jp112sdl/WemosD1_HomeMatic_StatusDisplay/Images/config_beispiel.png

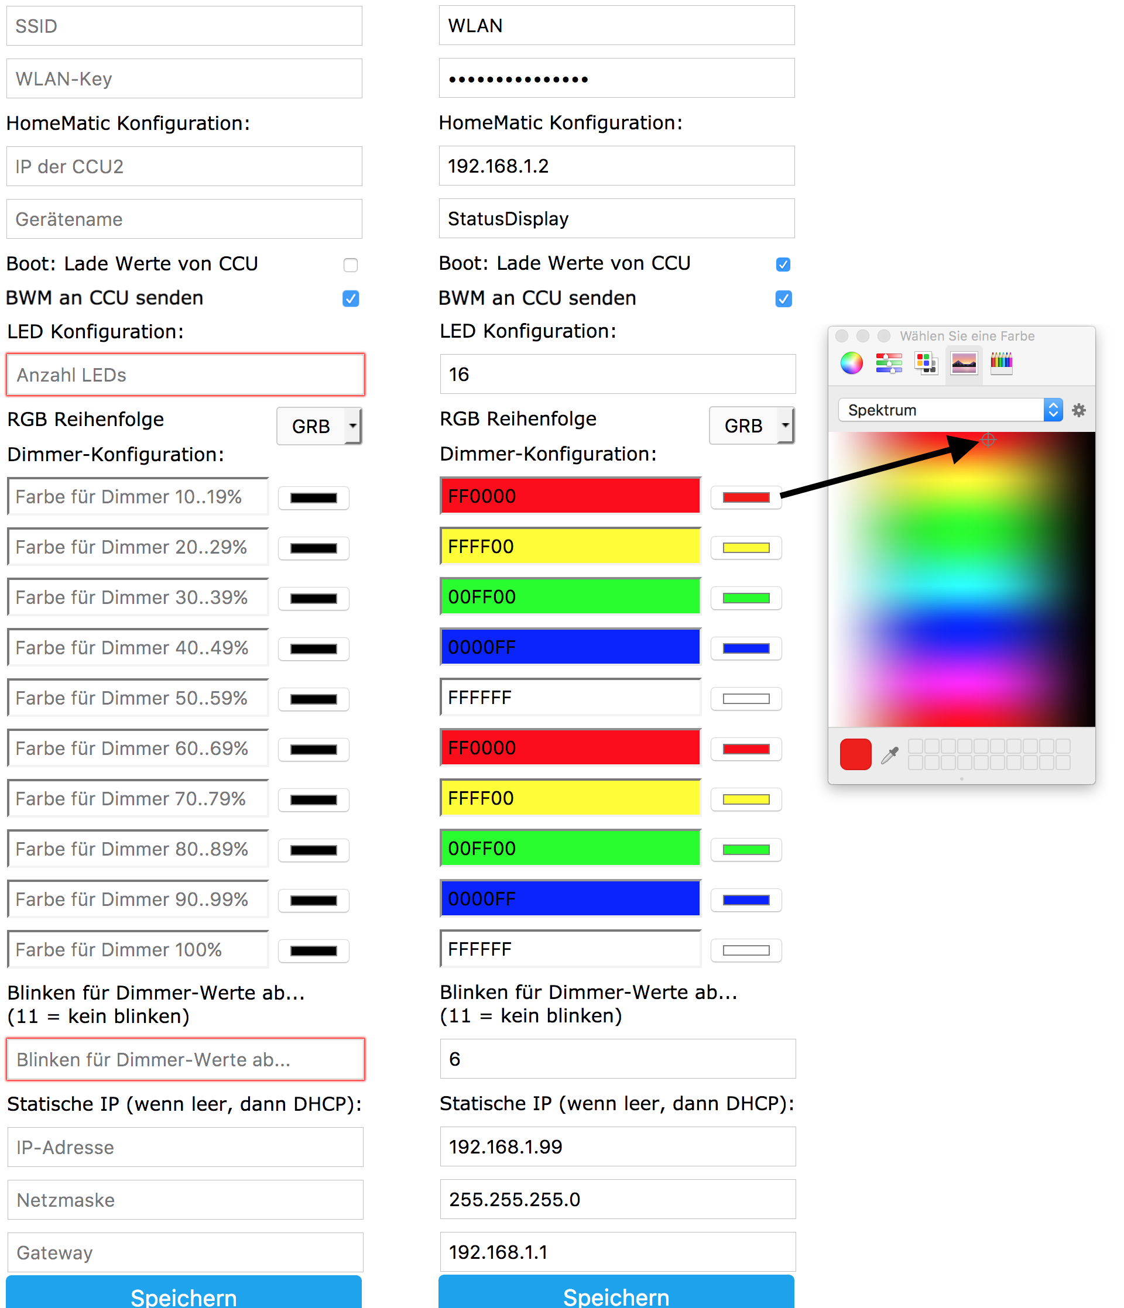
Images/config_beispiel.png
