jp112sdl/WemosD1_HomeMatic_StatusDisplay/Images/CUxD_Dimmer_erstellen.png

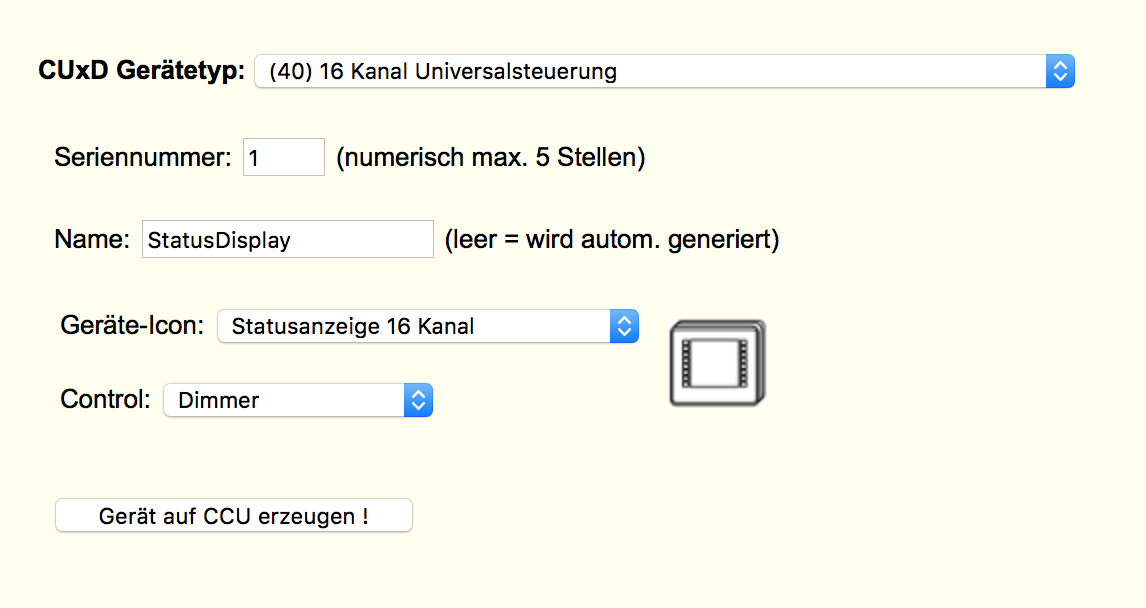
Images/CUxD_Dimmer_erstellen.png
