jp112sdl/WemosD1_HomeMatic_StatusDisplay/Images/CUxD_Exec_erstellen.png

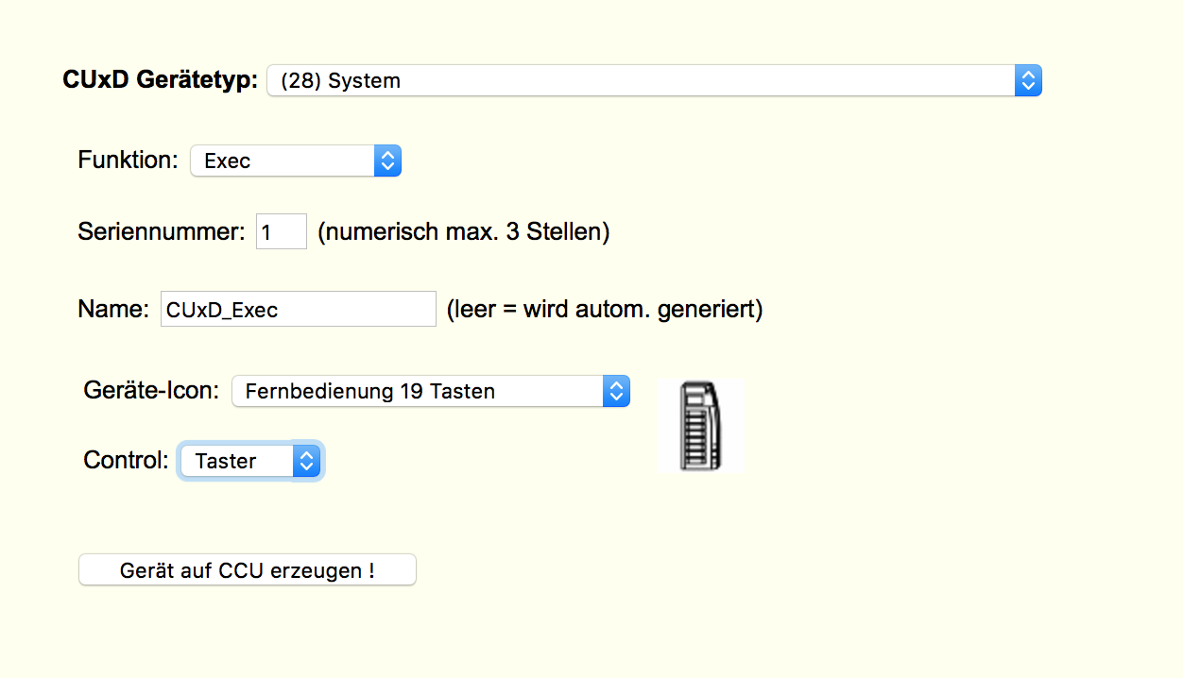
Images/CUxD_Exec_erstellen.png
