jp112sdl/WemosD1_HomeMatic_StatusDisplay/Images/mw/mw_back.jpg

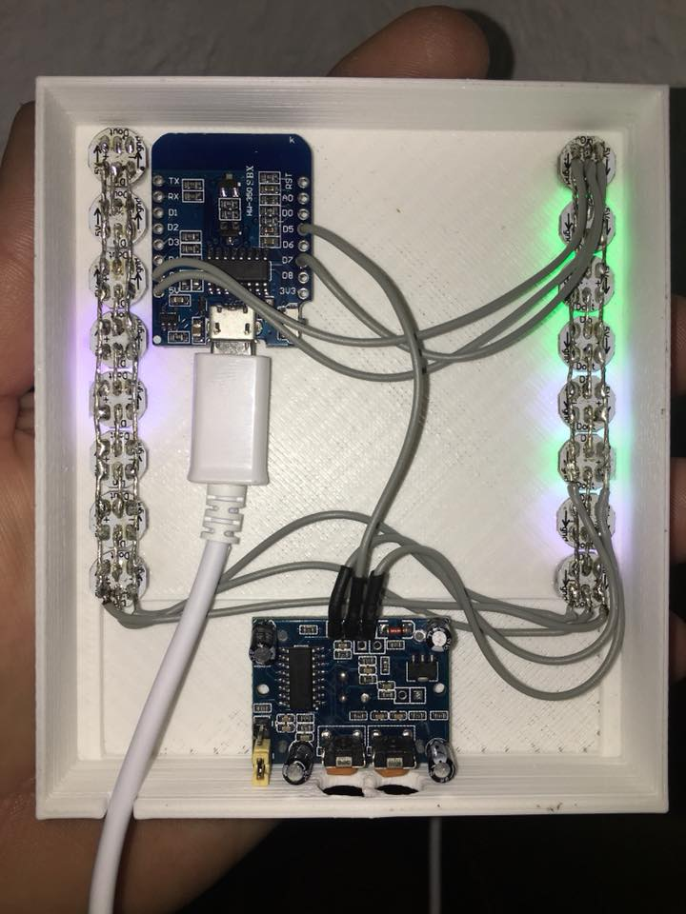
Images/mw/mw_back.jpg
