jp112sdl/WemosD1_HomeMatic_StatusDisplay/Images/mw/mw_pir.jpg

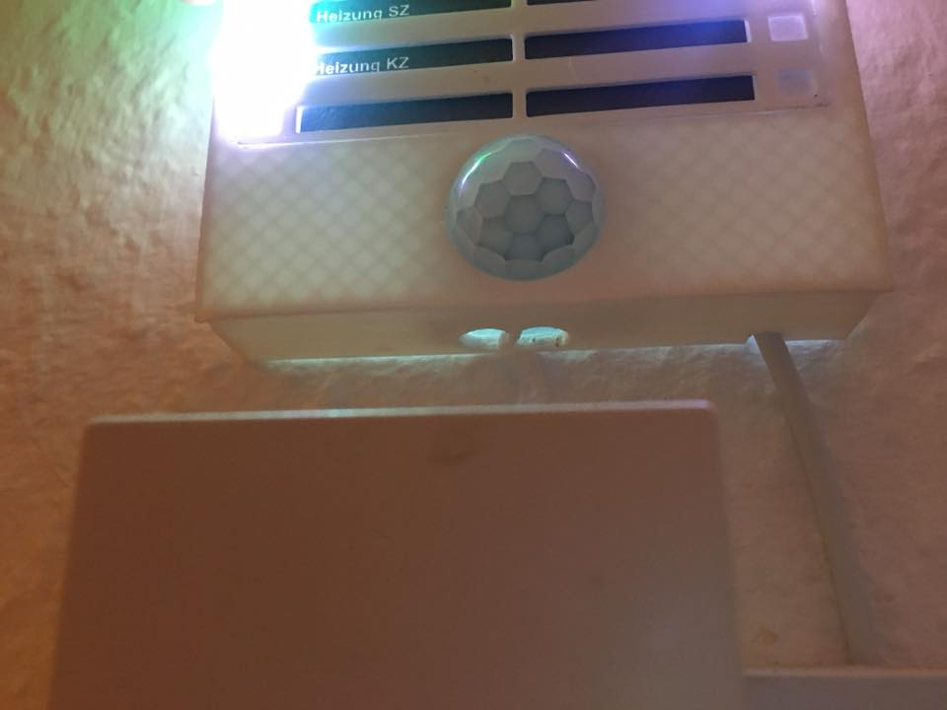
Images/mw/mw_pir.jpg
