jp112sdl/WemosD1_HomeMatic_StatusDisplay/Images/proto_side.jpg

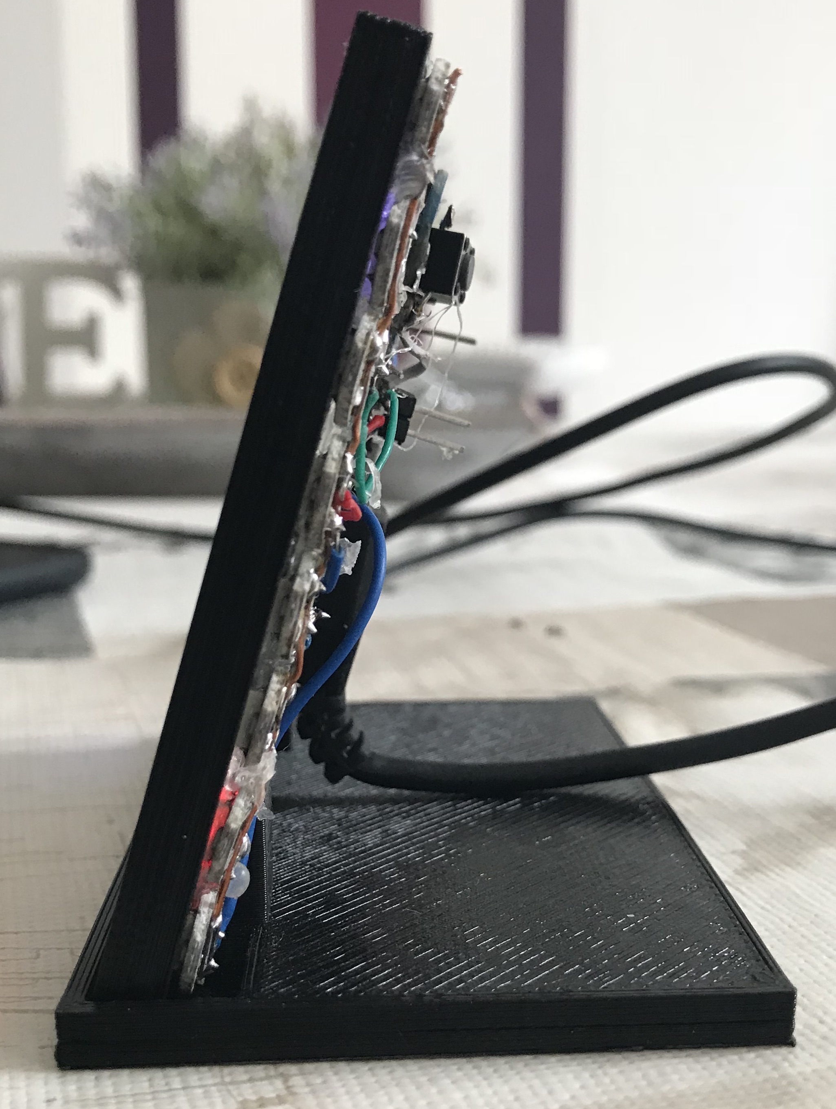
Images/proto_side.jpg
