jp112sdl/WemosD1_HomeMatic_StatusDisplay/Images/taster_config.jpg

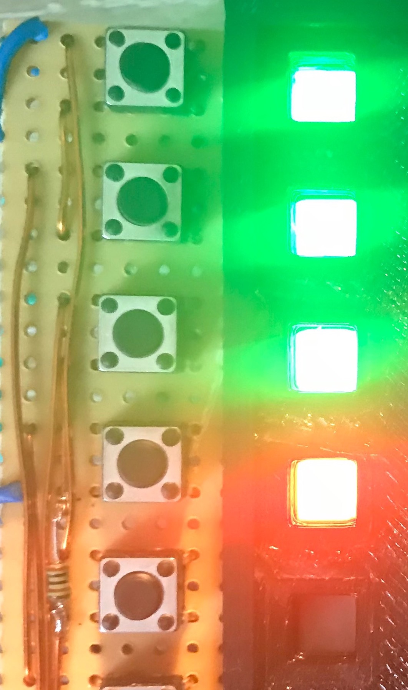
Images/taster_config.jpg
