jp112sdl/WemosD1_HomeMatic_StatusDisplay/Images/taster_cuxd40.png

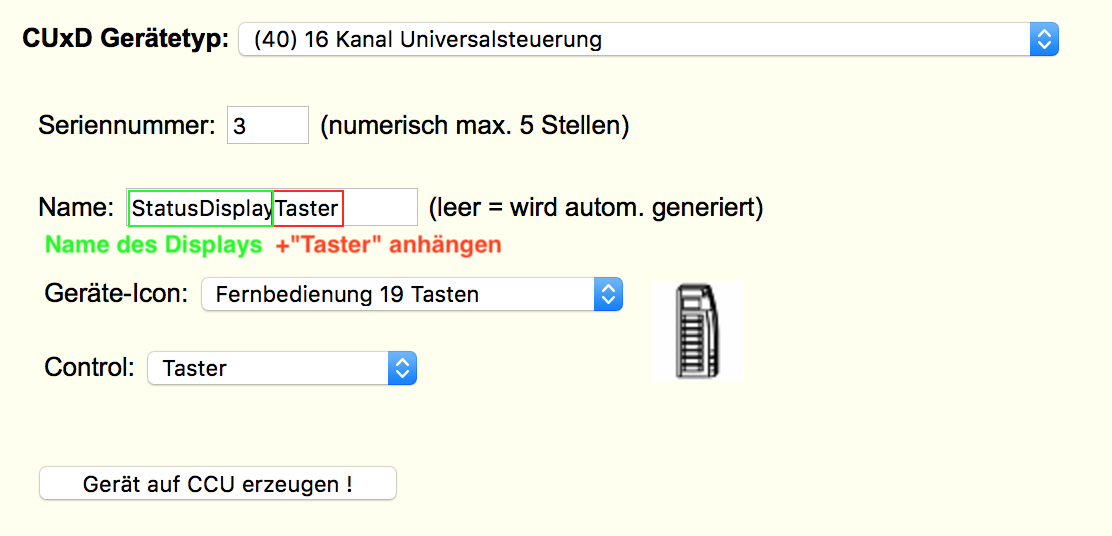
Images/taster_cuxd40.png
