jp112sdl/WemosD1_HomeMatic_StatusDisplay/Images/taster_programm.png

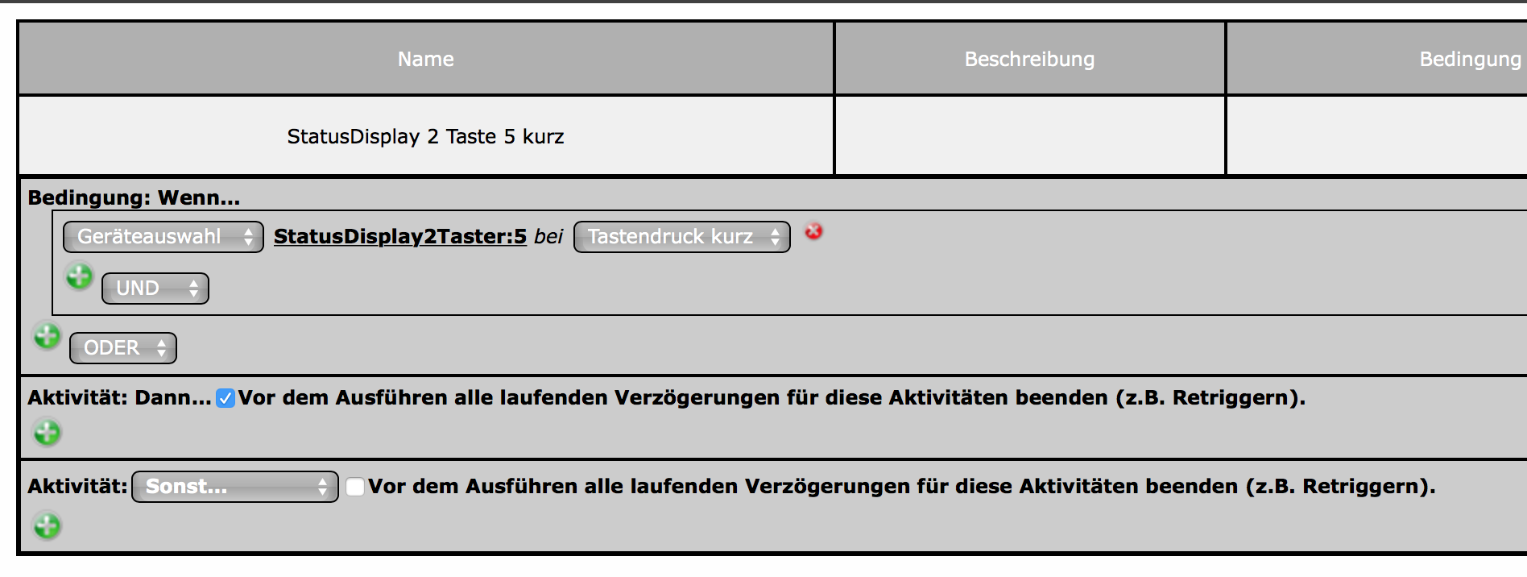
Images/taster_programm.png
