jp112sdl/WemosD1_HomeMatic_StatusDisplay/Images/WebUI_Programm.png

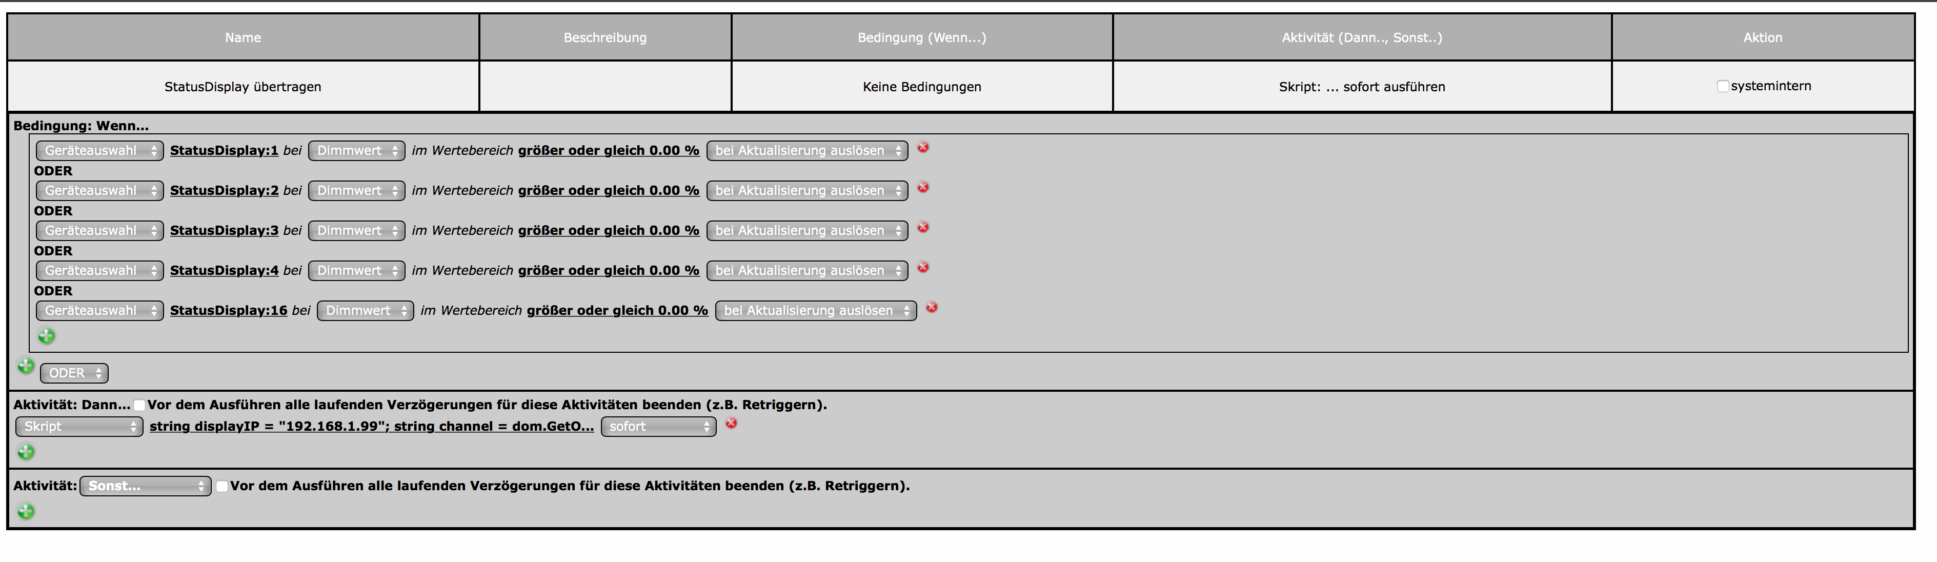
Images/WebUI_Programm.png
