jp112sdl/WemosD1_HomeMatic_StatusDisplay/Images/wiring.png

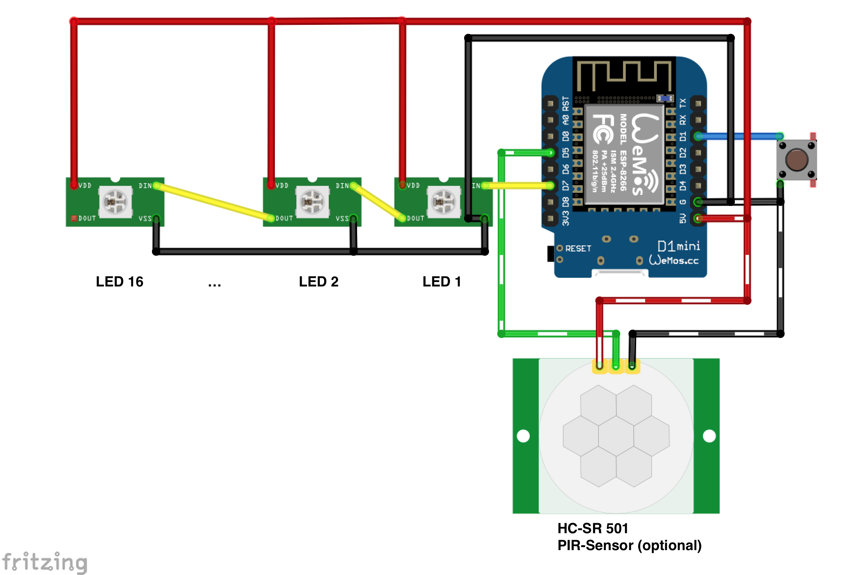
Images/wiring.png
