jp112sdl/WemosD1_HomeMatic_StatusDisplay/Images/wiring_taster.png

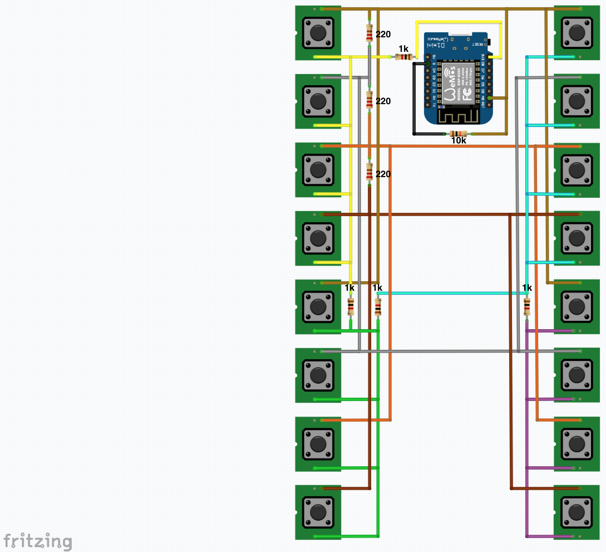
Images/wiring_taster.png
