jp112sdl/WemosD1_HomeMatic_StatusDisplay/Debug.ino

void DEBUG(String DebugMessage) {
  DEBUG(DebugMessage, "DummyTag",_slInformational);
}
void DEBUG(String DebugMessage, String Tag, byte Severity) {
#ifdef UDPDEBUG
  if (UDPReady) {
    UDPClient.UDP.beginPacket(SYSLOGIP, SYSLOGUDPPORT);
    byte severity = 8 + Severity;
    UDPClient.UDP.write(String("<" + String(severity) + ">" + String(GlobalConfig.DeviceName) + " " + Tag + " " + DebugMessage).c_str());
    UDPClient.UDP.endPacket();
  }
#endif

#ifdef SERIALDEBUG
  Serial.println(DebugMessage);
#endif
}
